kaihchang/Adept_BLE_3-pin/photos/PXL_20250902_035812439.jpg

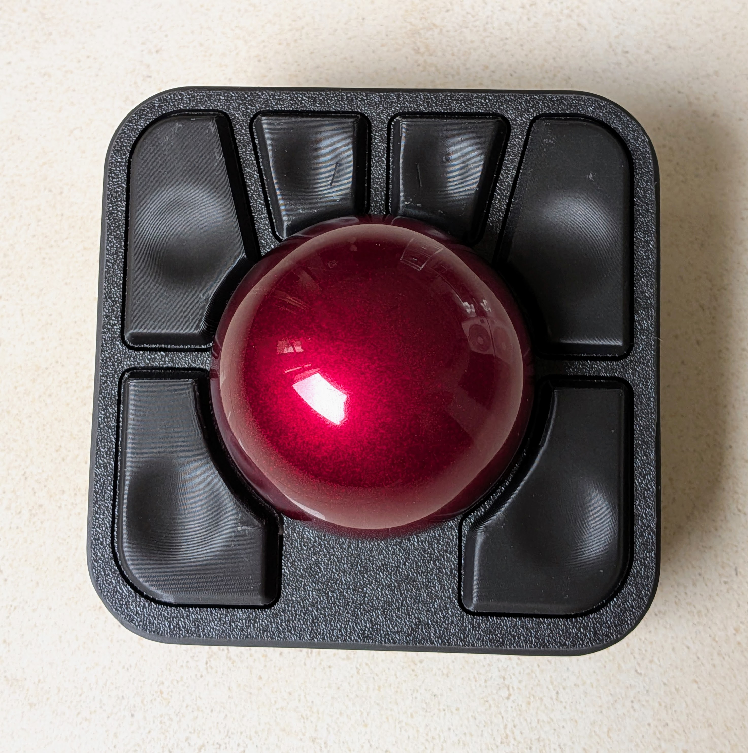
photos/PXL_20250902_035812439.jpg
