kaihchang/Adept_BLE_3-pin/photos/PXL_20250902_035908712.jpg

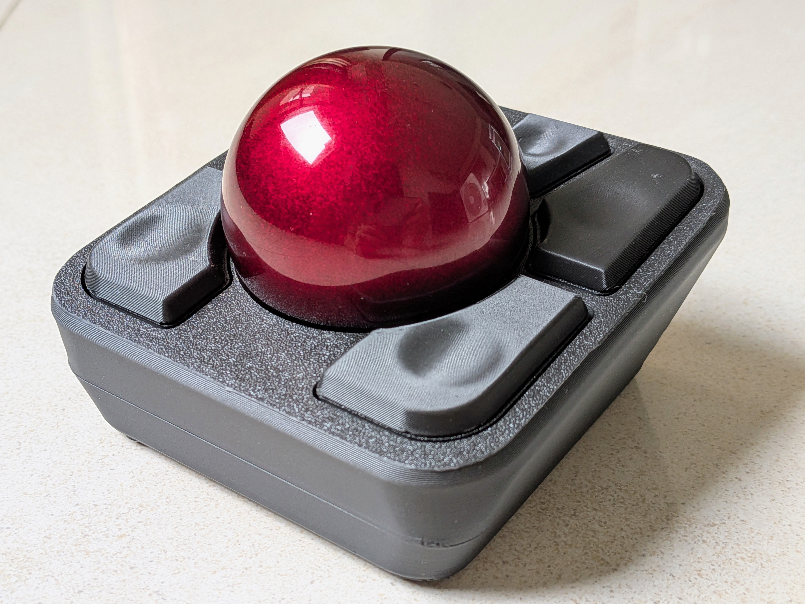
photos/PXL_20250902_035908712.jpg
