kaihchang/Adept_BLE_3-pin/photos/PXL_20250903_130032553.jpg

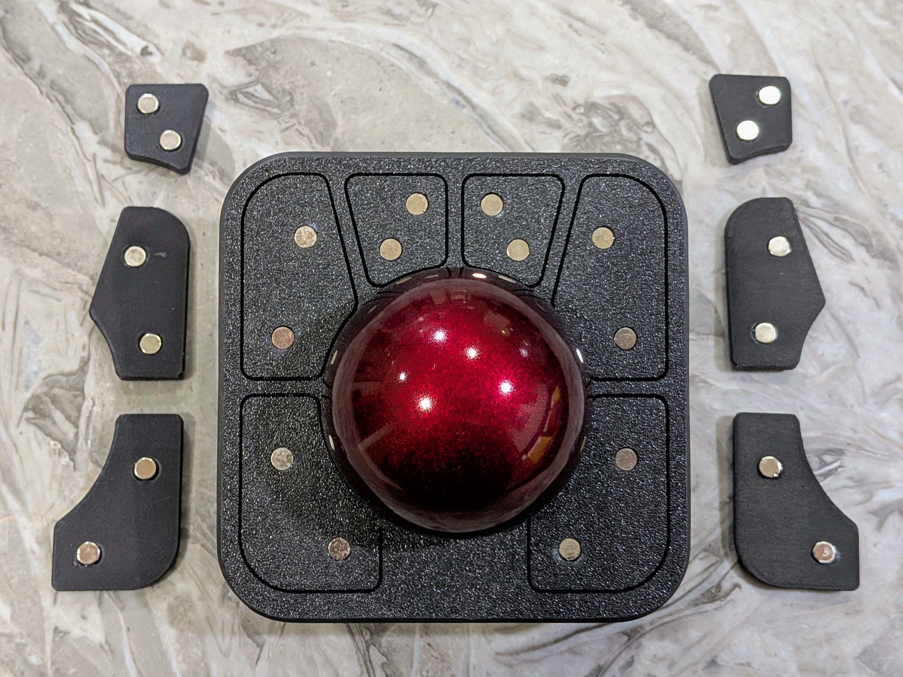
photos/PXL_20250903_130032553.jpg
